KaiPereira/M.2-FPGA-Accelerator/images/Pasted image 20251216200847.png

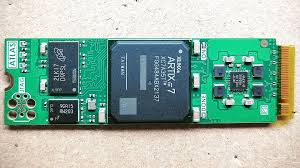
images/Pasted image 20251216200847.png
