KaiPereira/M.2-FPGA-Accelerator/PCB/renders/Bottom PCB Render Transparent.png

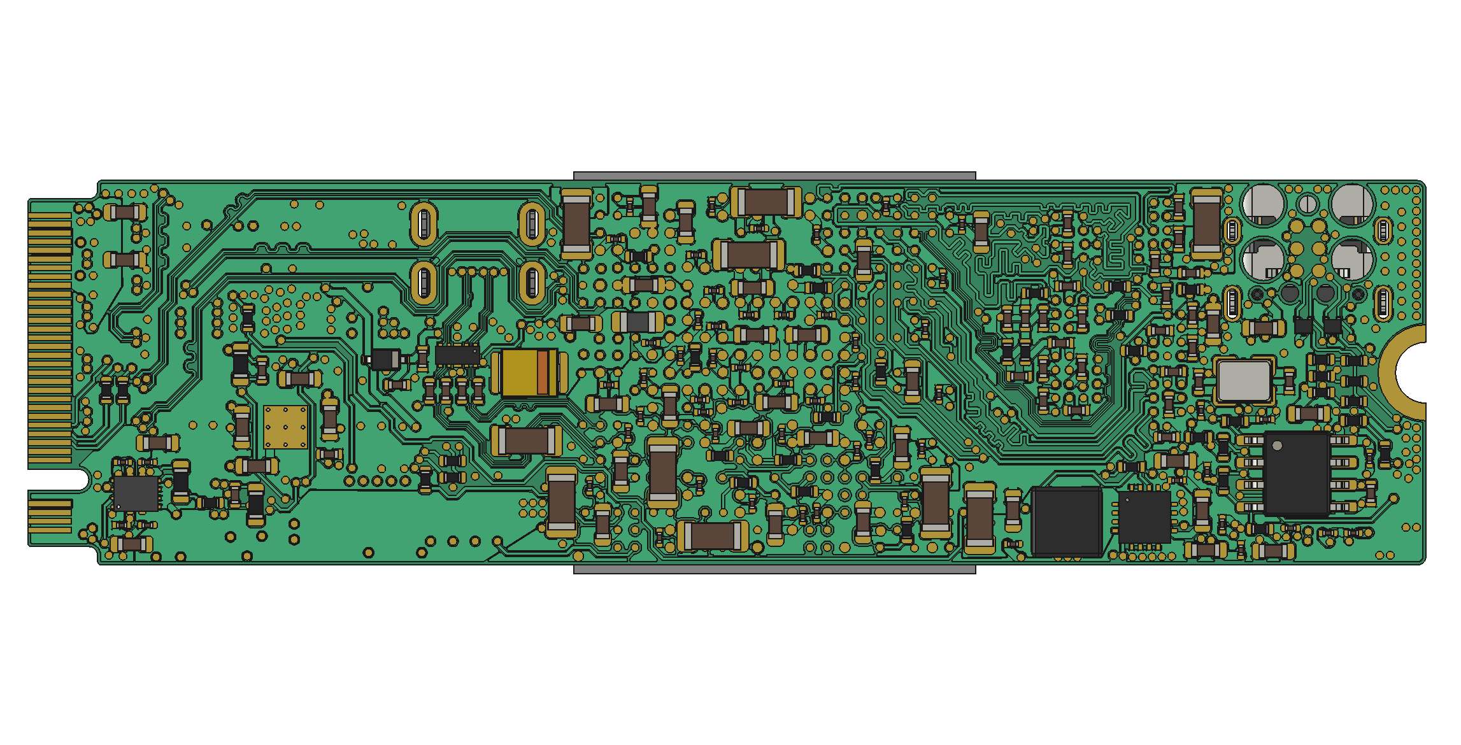
PCB/renders/Bottom PCB Render Transparent.png
