KaiPereira/M.2-FPGA-Accelerator/PCB/renders/Top PCB Render Transparent.png

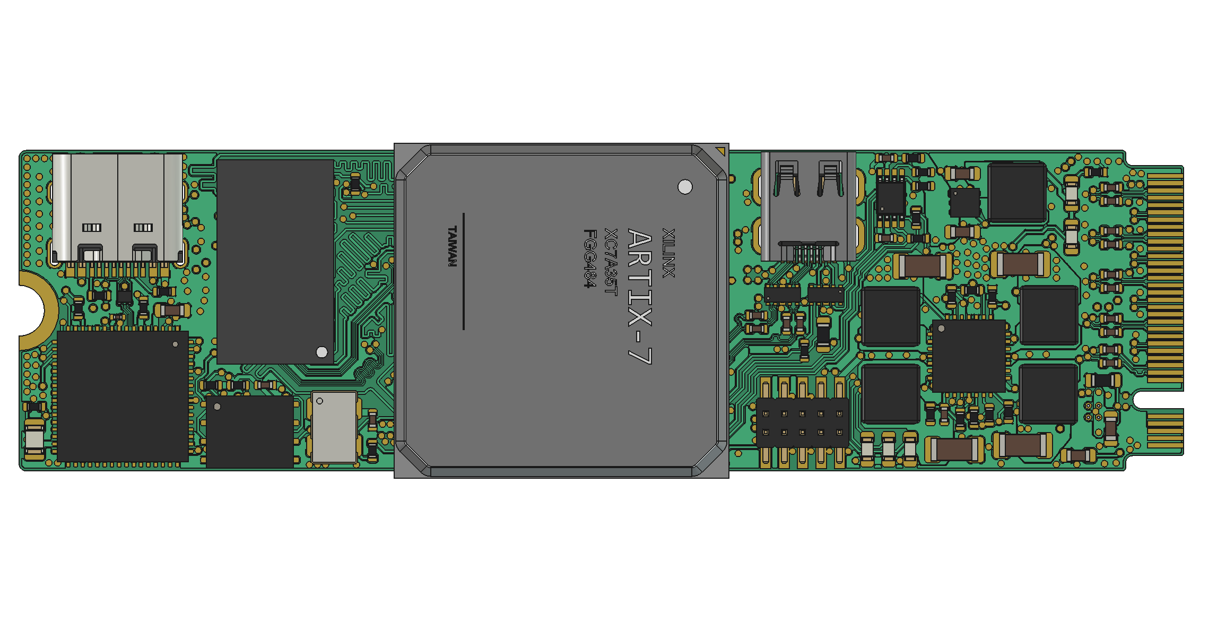
PCB/renders/Top PCB Render Transparent.png
